openenergymonitor/emonpi/firmware/emonPi_DS_jeelib_classic/interrupt.ino

// The interrupt routine - runs each time a falling edge of a pulse is detected
void onPulse()                  
{  
  if ( (millis() - pulsetime) > min_pulsewidth) {
    pulseCount++;					//calculate wh elapsed from time between pulses 
  }
 pulsetime=millis(); 	
}
